The8BitEnthusiast/apple-1-video-terminal-on-fpga/schematics/fpga-8-bit-cpu-interface/fpga-8-bit-cpu-interface.kicad_pcb

## KiCad design Kicad/oled_unicorny.kicad_pcb

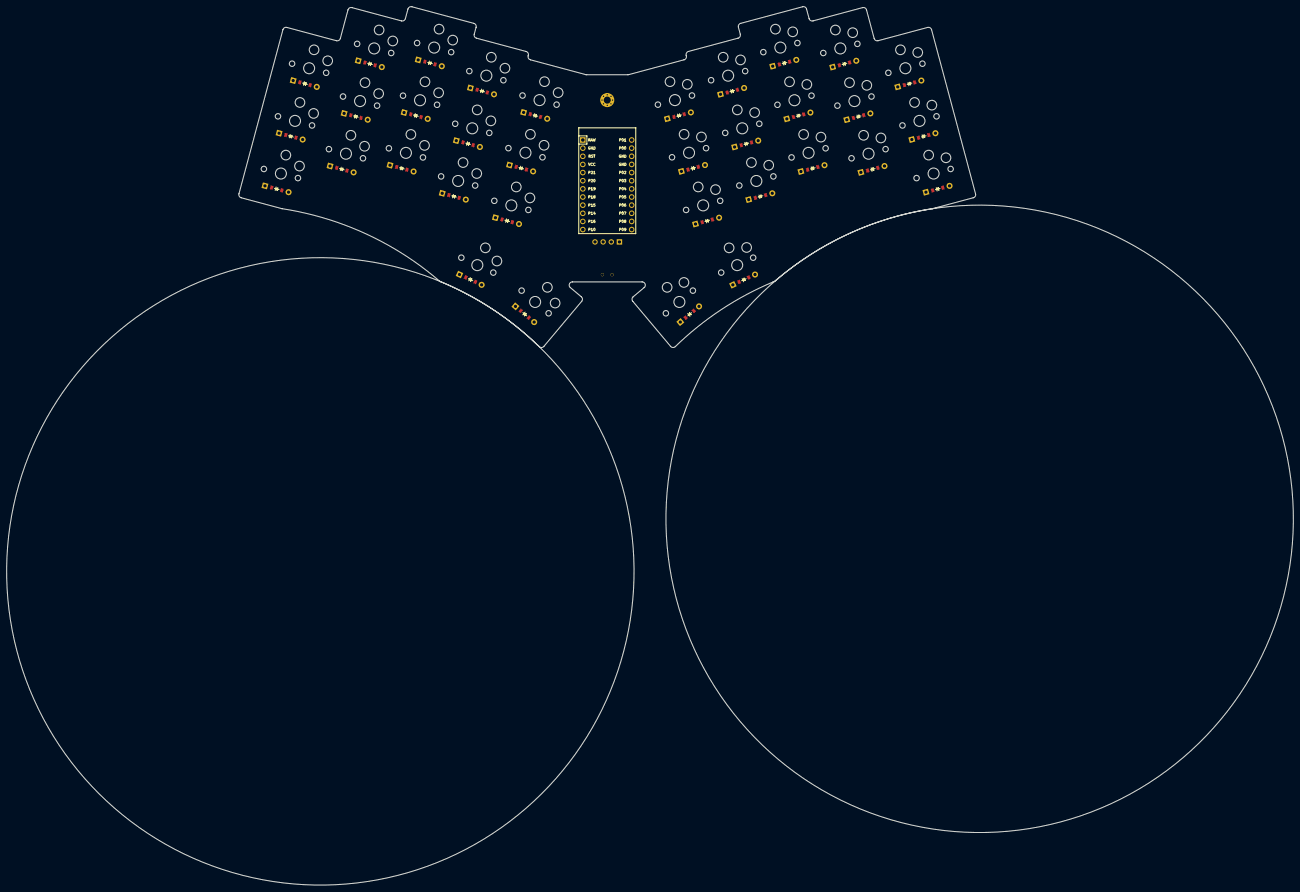
[picture p8: board oled_unicorny.kicad_pcb from above]

Board: 2 copper layers, 401.3 x 274.0 mm, 74 parts (0 on the bottom side), 52 nets, no tracks yet.

Parts:
D1, D2, D3, D4, D5, D6, D7, D8, D9, D10, D11, D12, D13, D14, D15, D16, D17, D18, D19, D20, D21, D22, D23, D24, D25, D26, D27, D28, D29, D30, D31, D32, D33, D34: ComboDiode
MCU1: ProMicro
OLED1: OLED; OLED_headers
PAD1, PAD2: SMDPad
S1, S2, S3, S4, S5, S6, S7, S8, S9, S10, S11, S12, S13, S14, S15, S16, S17, S18, S19, S20, S21, S22, S23, S24, S25, S26, S27, S28, S29, S30, S31, S32, S33, S34: PG1350
T1: SPDT_C128955
_1: MountingHole_2.2mm_M2_Pad_Via

Connections:
B+: PAD1.1, T1.2
GND: MCU1.2, MCU1.15, MCU1.16, OLED1.1, PAD2.1
P0: MCU1.14, S10.1, S11.1, S12.1, S16.1, S27.1, S28.1, S29.1, S33.1
P1: MCU1.13, S13.1, S14.1, S15.1, S17.1, S30.1, S31.1, S32.1, S34.1
P2: MCU1.17, OLED1.4
P3: MCU1.18, OLED1.3
P6: D20.1, D23.1, D26.1, D29.1, D32.1, MCU1.21
P7: D19.1, D22.1, D25.1, D28.1, D31.1, MCU1.22
P8: D18.1, D21.1, D24.1, D27.1, D30.1, MCU1.23
P14: D1.1, D4.1, D7.1, D10.1, D13.1, MCU1.10
P15: D2.1, D5.1, D8.1, D11.1, D14.1, MCU1.9
P16: D16.1, D17.1, D33.1, D34.1, MCU1.11
P18: D3.1, D6.1, D9.1, D12.1, D15.1, MCU1.8
P19: MCU1.7, S1.1, S2.1, S3.1, S18.1, S19.1, S20.1
P20: MCU1.6, S4.1, S5.1, S6.1, S21.1, S22.1, S23.1
P21: MCU1.5, S7.1, S8.1, S9.1, S24.1, S25.1, S26.1
RAW: MCU1.1, T1.1
VCC: MCU1.4, OLED1.2
index_bottom: D10.2, S10.2
index_home: D11.2, S11.2
index_top: D12.2, S12.2
inner_bottom: D13.2, S13.2
inner_home: D14.2, S14.2
inner_top: D15.2, S15.2
middle_bottom: D7.2, S7.2
middle_home: D8.2, S8.2
middle_top: D9.2, S9.2
mirror_index_bottom: D27.2, S27.2
mirror_index_home: D28.2, S28.2
mirror_index_top: D29.2, S29.2
mirror_inner_bottom: D30.2, S30.2
mirror_inner_home: D31.2, S31.2
mirror_inner_top: D32.2, S32.2
mirror_middle_bottom: D24.2, S24.2
mirror_middle_home: D25.2, S25.2
mirror_middle_top: D26.2, S26.2
mirror_pinky_bottom: D18.2, S18.2
mirror_pinky_home: D19.2, S19.2
mirror_pinky_top: D20.2, S20.2
mirror_reachy_fan: D34.2, S34.2
mirror_ring_bottom: D21.2, S21.2
mirror_ring_home: D22.2, S22.2
mirror_ring_top: D23.2, S23.2
mirror_tucky_fan: D33.2, S33.2
pinky_bottom: D1.2, S1.2
pinky_home: D2.2, S2.2
pinky_top: D3.2, S3.2
reachy_fan: D17.2, S17.2
ring_bottom: D4.2, S4.2
ring_home: D5.2, S5.2
ring_top: D6.2, S6.2
tucky_fan: D16.2, S16.2
