The8BitEnthusiast/apple-1-video-terminal-on-fpga/src/verilog/top_8bit_cpu.v

`timescale 1ns / 1ps
//////////////////////////////////////////////////////////////////////////////////
// Company: 
// Engineer: 
// 
// Create Date: 03/18/2022 12:20:01 PM
// Design Name: 
// Module Name: top
// Project Name: Apple 1 Video Terminal Display 
// Target Devices: 
// Tool Versions: 
// Description: 
// 
// Dependencies: 
// 
// Revision:
// Revision 0.01 - File Created
// Additional Comments:
// Instantiation:
// 
//////////////////////////////////////////////////////////////////////////////////

module top_8bit_cpu(
    input clk,
    input [7:1] rd,
    input da,
    output rda,
    input clr_btn,
    output vid1,
    output vid2,
    output heartbeat
    );

    wire clk_out;
    wire clk_locked;
    wire locked;
    
    wire rda_n;
    wire da_out;
    
    assign rda = ~rda_n;

    clk_gen clk0 (.clk_in(clk), .clk_out(clk_out), .locked(locked));

    assign clk_locked = clk_out & locked;
    
    // this register acts as the PIA for the 8-bit CPU
    ic_74273 reg0 (.d({1'b1, rd[7:1]}), 
        .q({da_out, 7'b0000000}), .mr_n(rda_n), .cp(da));

    video_terminal vt0 (.clk(clk_locked), 
        .rd(rd), 
        .da(da_out), 
        .clr_btn(clr_btn),
        .rda_n(rda_n), 
        .vid1(vid1), 
        .vid2(vid2),
        .heartbeat(hearbeat));

endmodule
