The8BitEnthusiast/apple-1-video-terminal-on-fpga/src/verilog/ic_2513.v

`timescale 1ns / 1ps
//////////////////////////////////////////////////////////////////////////////////
// Company: 
// Engineer: 
// 
// Create Date: 03/21/2022 09:35:45 AM
// Design Name: 
// Module Name: ic_2513 
// Project Name: 
// Target Devices: 
// Tool Versions: 
// Description: 64 X 8 X 5 Character Generator 
// 
// Dependencies: 
// 
// Revision:
// Revision 0.01 - File Created
// Additional Comments:
// Instantation:
//     ic_2513 u0 ( .x(), .a() );
// 
//////////////////////////////////////////////////////////////////////////////////


module ic_2513(
    output reg [5:1] x,
    input [9:1] a
    );
    
    always @ (a)
    begin
        case ( a )
            // character '@'
            9'b000000000 : x = 5'b00000 ;
            9'b000000001 : x = 5'b01110 ;
            9'b000000010 : x = 5'b10001 ;
            9'b000000011 : x = 5'b10101 ;
            9'b000000100 : x = 5'b10111 ;
            9'b000000101 : x = 5'b10110 ;
            9'b000000110 : x = 5'b10000 ;
            9'b000000111 : x = 5'b01111 ;

            // character 'A'
            9'b000001000 : x = 5'b00000 ;
            9'b000001001 : x = 5'b00100 ;
            9'b000001010 : x = 5'b01010 ;
            9'b000001011 : x = 5'b10001 ;
            9'b000001100 : x = 5'b10001 ;
            9'b000001101 : x = 5'b11111 ;
            9'b000001110 : x = 5'b10001 ;
            9'b000001111 : x = 5'b10001 ;

             // character 'B'
            9'b000010000 : x = 5'b00000 ;
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
            9'b111111010 : x = 5'b10001 ;
            9'b111111011 : x = 5'b00010 ;
            9'b111111100 : x = 5'b00100 ;
            9'b111111101 : x = 5'b00100 ;
            9'b111111110 : x = 5'b00000 ;
            9'b111111111 : x = 5'b00100 ;

      endcase
    end

endmodule
