The8BitEnthusiast/apple-1-video-terminal-on-fpga/src/verilog/ic_2504.v

`timescale 1ns / 1ps
//////////////////////////////////////////////////////////////////////////////////
// Company: 
// Engineer: 
// 
// Create Date: 05/03/2022 05:14:17 PM
// Design Name: 
// Module Name: ic_2504
// Project Name: Apple 1 Video Display Terminal
// Target Devices: 
// Tool Versions: 
// Description: A Verilog implementation of the Signetics 2504 Shift Register 
// 
// Dependencies: 
// 
// Revision:
// Revision 0.01 - File Created
// Additional Comments:
// Instantation: ic_2504 u0 ( .clk(), .si(), .so() );
// 
//////////////////////////////////////////////////////////////////////////////////

module ic_2504(
    input clk,
    input si,
    output so
    );
    
    reg [1023:0] tmp;
    
    always @(posedge clk)
    begin
        tmp <= {tmp[1022:0], si};
    end
    
    assign so = tmp[1023];

    // simulation initial state
    initial begin
        tmp <= 0;
    end
    
endmodule
