The8BitEnthusiast/apple-1-video-terminal-on-fpga/src/verilog/ic_555.v

`timescale 1ns / 1ps
//////////////////////////////////////////////////////////////////////////////////
// Company: 
// Engineer: 
// 
// Create Date: 01/26/2023 12:40:10 PM
// Design Name: 
// Module Name: blinky
// Project Name: 
// Target Devices: 
// Tool Versions: 
// Description: 
// 
// Dependencies: 
// 
// Revision:
// Revision 0.01 - File Created
// Additional Comments:
// Instantiation:
//     ic_555 timer0 ( .clk(), .out() );
// 
//////////////////////////////////////////////////////////////////////////////////


module ic_555(
    input clk,
    output out
    );
    
    reg [23:0] count = 0;
    
    assign out = count[23];
    
    always @ (posedge(clk)) count <= count + 1;
    
endmodule
